clockworkpi/DevTerm/Clockwork_DevTerm_DIY_Graphene_Heat_Sink.pdf

A

+ | =

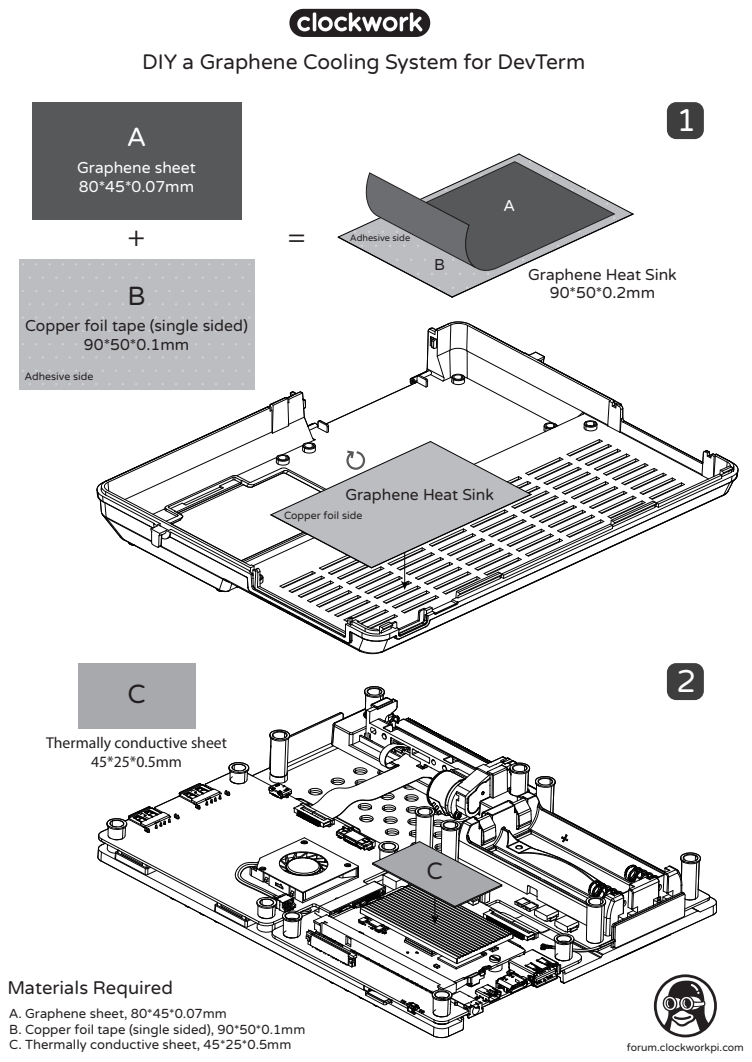
[picture p36: page 1]
Adhesive side; Graphene sheet 80*45*0.07mm; C. Thermally conductive sheet, 45*25*0.5mm; forum.clockworkpi.com

DIY a Graphene Cooling System for DevTerm

Graphene Heat Sink

Copper foil tape (single sided)

Copper foil side

Thermally conductive sheet

Materials Required
A. Graphene sheet, 80*45*0.07mm
B. Copper foil tape (single sided), 90*50*0.1mm
