clockworkpi/DevTerm/Code/thermal_printer/logo.h

#ifndef LOGO_H
#define LOGO_H

#define os120_width 120
#define os120_height 120

const unsigned char os120_bits[] = {
   0x00, 0x00, 0x00, 0x00, 0x00, 0x00, 0x00, 0x00, 0x00, 0x00, 0x00, 0x00,
   0x00, 0x00, 0x00, 0x00, 0x00, 0x00, 0x00, 0x00, 0x00, 0xf8, 0xff, 0x1f,
   0x00, 0x00, 0x00, 0x00, 0x00, 0x00, 0x00, 0x00, 0x00, 0x00, 0x00, 0xc0,
   0xff, 0xff, 0xff, 0x03, 0x00, 0x00, 0x00, 0x00, 0x00, 0x00, 0x00, 0x00,
   0x00, 0x00, 0xfc, 0xff, 0xff, 0xff, 0x3f, 0x00, 0x00, 0x00, 0x00, 0x00,
   0x00, 0x00, 0x00, 0x00, 0x80, 0xff, 0xff, 0xff, 0xff, 0xff, 0x01, 0x00,
   0x00, 0x00, 0x00, 0x00, 0x00, 0x00, 0x00, 0xe0, 0xff, 0xff, 0xff, 0xff,
   0xff, 0x07, 0x00, 0x00, 0x00, 0x00, 0x00, 0x00, 0x00, 0x00, 0xf8, 0xff,
   0x1f, 0x00, 0xf8, 0xff, 0x1f, 0x00, 0x00, 0x00, 0x00, 0x00, 0x00, 0x00,
   0x00, 0xfe, 0x7f, 0x00, 0x00, 0x00, 0xfe, 0x7f, 0x00, 0x00, 0x00, 0x00,
   0x00, 0x00, 0x00, 0x80, 0xff, 0x0f, 0x00, 0x00, 0x00, 0xf0, 0xff, 0x01,
   0x00, 0x00, 0x00, 0x00, 0x00, 0x00, 0xe0, 0xff, 0x01, 0x00, 0x00, 0x00,
   0x80, 0xff, 0x07, 0x00, 0x00, 0x00, 0x00, 0x00, 0x00, 0xf8, 0x3f, 0x00,
   0x00, 0x00, 0x00, 0x00, 0xfc, 0x1f, 0x00, 0x00, 0x00, 0x00, 0x00, 0x00,
   0xfc, 0x0f, 0x00, 0x00, 0x00, 0x00, 0x00, 0xf0, 0x3f, 0x00, 0x00, 0x00,
   0x00, 0x00, 0x00, 0xfe, 0x03, 0x00, 0x00, 0xf8, 0x01, 0x00, 0xc0, 0x7f,
   0x00, 0x00, 0x00, 0x00, 0x00, 0x80, 0xff, 0x01, 0x00, 0xf0, 0xff, 0xff,
   0x00, 0x80, 0xff, 0x01, 0x00, 0x00, 0x00, 0x00, 0xc0, 0x7f, 0x00, 0x00,
   0xff, 0xff, 0xff, 0x07, 0x00, 0xfe, 0x03, 0x00, 0x00, 0x00, 0x00, 0xe0,
   0x1f, 0x00, 0xe0, 0xff, 0xff, 0xff, 0x3f, 0x00, 0xf8, 0x07, 0x00, 0x00,
   0x00, 0x00, 0xf0, 0x0f, 0x00, 0xf8, 0xff, 0xff, 0xff, 0xff, 0x00, 0xf0,
   0x0f, 0x00, 0x00, 0x00, 0x00, 0xf8, 0x07, 0x00, 0xfe, 0xff, 0xff, 0xff,
   0xff, 0x01, 0xe0, 0x1f, 0x00, 0x00, 0x00, 0x00, 0xfc, 0x01, 0x00, 0xff,
   0xff, 0xff, 0xff, 0xff, 0x07, 0x80, 0x3f, 0x00, 0x00, 0x00, 0x00, 0xfe,
   0x00, 0xc0, 0xff, 0xff, 0xff, 0x7f, 0xfc, 0x0f, 0x00, 0x7f, 0x00, 0x00,
   0x00, 0x00, 0x7f, 0x00, 0xe0, 0xff, 0xff, 0xff, 0x3f, 0xf0, 0x1f, 0x00,
   0xfe, 0x00, 0x00, 0x00, 0x80, 0x3f, 0x00, 0xf0, 0xff, 0xff, 0xff, 0x3f,
   0xe0, 0x3f, 0x00, 0xfc, 0x01, 0x00, 0x00, 0xc0, 0x1f, 0x00, 0xf8, 0xff,
   0xff, 0xff, 0x7f, 0x80, 0x7f, 0x00, 0xf8, 0x03, 0x00, 0x00, 0xe0, 0x0f,
   0x00, 0xfc, 0xff, 0xff, 0xff, 0xff, 0x01, 0x7f, 0x00, 0xf0, 0x07, 0x00,
   0x00, 0xe0, 0x07, 0x00, 0xfc, 0xff, 0xff, 0xff, 0xff, 0x07, 0xfe, 0x00,
   0xe0, 0x07, 0x00, 0x00, 0xf0, 0x03, 0x00, 0xfe, 0xff, 0xff, 0xff, 0xff,
   0x0f, 0xfc, 0x01, 0xc0, 0x0f, 0x00, 0x00, 0xf8, 0x03, 0x00, 0xff, 0xff,
   0xff, 0xff, 0xff, 0x1f, 0xfc, 0x01, 0xc0, 0x1f, 0x00, 0x00, 0xfc, 0x01,
   0x00, 0xff, 0xff, 0xff, 0xff, 0xff, 0x3f, 0xf8, 0x03, 0x80, 0x3f, 0x00,
   0x00, 0xfc, 0x00, 0x80, 0xff, 0xff, 0xff, 0xff, 0xff, 0x7f, 0xf0, 0x07,
   0x00, 0x3f, 0x00, 0x00, 0x7e, 0x00, 0x80, 0xff, 0xff, 0xff, 0xff, 0xff,
   0xff, 0xf0, 0x07, 0x00, 0x7e, 0x00, 0x00, 0x7e, 0x00, 0xc0, 0xff, 0xff,
   0xff, 0xff, 0xff, 0xff, 0xf0, 0x07, 0x00, 0x7e, 0x00, 0x00, 0x3f, 0x00,
   0xc0, 0xff, 0xff, 0xff, 0xff, 0xff, 0xff, 0xf9, 0x0f, 0x00, 0xfc, 0x00,
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


#endif
