clockworkpi/DevTerm/Code/thermal_printer/pcf_5x7-ISO8859-1_5x7.h

#ifndef FONT_PCF_5X7_ISO8859_1_5X7_H
#define FONT_PCF_5X7_ISO8859_1_5X7_H

const unsigned char font_pcf_5x7_ISO8859_1_5x7[]   = {

    /*
     * code=0, hex=0x00, ascii="^@"
     */
    0x00,  /* 00000 */
    0xA8,  /* 10101 */
    0x00,  /* 00000 */
    0x88,  /* 10001 */
    0x00,  /* 00000 */
    0xA8,  /* 10101 */
    0x00,  /* 00000 */

    /*
     * code=1, hex=0x01, ascii="^A"
     */
    0x00,  /* 00000 */
    0x20,  /* 00100 */
    0x70,  /* 01110 */
    0xF8,  /* 11111 */
    0x70,  /* 01110 */
    0x20,  /* 00100 */
    0x00,  /* 00000 */

    /*
     * code=2, hex=0x02, ascii="^B"
     */
    0xA8,  /* 10101 */
    0x50,  /* 01010 */
    0xA8,  /* 10101 */
    0x50,  /* 01010 */
    0xA8,  /* 10101 */
    0x50,  /* 01010 */
    0xA8,  /* 10101 */

    /*
     * code=3, hex=0x03, ascii="^C"
     */
    0xA0,  /* 10100 */
    0xE0,  /* 11100 */
    0xA0,  /* 10100 */
    0x70,  /* 01110 */
    0x20,  /* 00100 */
    0x20,  /* 00100 */
    0x00,  /* 00000 */

    /*
     * code=4, hex=0x04, ascii="^D"
     */
    0xE0,  /* 11100 */
    0x80,  /* 10000 */
    0xF8,  /* 11111 */
    0xA0,  /* 10100 */
    0x30,  /* 00110 */
    0x20,  /* 00100 */
    0x00,  /* 00000 */

    /*
     * code=5, hex=0x05, ascii="^E"
     */
    0x60,  /* 01100 */
    0x80,  /* 10000 */
    0xE0,  /* 11100 */
    0x50,  /* 01010 */
    0x60,  /* 01100 */
    0x50,  /* 01010 */
    0x00,  /* 00000 */

    /*
     * code=6, hex=0x06, ascii="^F"
     */
    0x80,  /* 10000 */
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
    0x00,  /* 00000 */
    0xA8,  /* 10101 */
    0x00,  /* 00000 */

    /*
     * code=254, hex=0xFE, ascii="!~"
     */
    0x00,  /* 00000 */
    0xA8,  /* 10101 */
    0x00,  /* 00000 */
    0x88,  /* 10001 */
    0x00,  /* 00000 */
    0xA8,  /* 10101 */
    0x00,  /* 00000 */

    /*
     * code=255, hex=0xFF, ascii="!^Ÿ"
     */
    0x00,  /* 00000 */
    0xA8,  /* 10101 */
    0x00,  /* 00000 */
    0x88,  /* 10001 */
    0x00,  /* 00000 */
    0xA8,  /* 10101 */
    0x00,  /* 00000 */
};

#endif
