clockworkpi/DevTerm/Code/thermal_printer/pcf_6x12-ISO8859-1_6x12.h

#ifndef FONT_PCF_6X12_ISO8859_1_6X12_H
#define FONT_PCF_6X12_ISO8859_1_6X12_H

const unsigned char font_pcf_6x12_ISO8859_1_6x12[] = {

    /*
     * code=0, hex=0x00, ascii="^@"
     */
    0x00,  /* 000000 */
    0x00,  /* 000000 */
    0x00,  /* 000000 */
    0xA8,  /* 101010 */
    0x00,  /* 000000 */
    0x88,  /* 100010 */
    0x00,  /* 000000 */
    0x88,  /* 100010 */
    0x00,  /* 000000 */
    0xA8,  /* 101010 */
    0x00,  /* 000000 */
    0x00,  /* 000000 */

    /*
     * code=1, hex=0x01, ascii="^A"
     */
    0x00,  /* 000000 */
    0x00,  /* 000000 */
    0x00,  /* 000000 */
    0x00,  /* 000000 */
    0x20,  /* 001000 */
    0x70,  /* 011100 */
    0xF8,  /* 111110 */
    0x70,  /* 011100 */
    0x20,  /* 001000 */
    0x00,  /* 000000 */
    0x00,  /* 000000 */
    0x00,  /* 000000 */

    /*
     * code=2, hex=0x02, ascii="^B"
     */
    0xA8,  /* 101010 */
    0x54,  /* 010101 */
    0xA8,  /* 101010 */
    0x54,  /* 010101 */
    0xA8,  /* 101010 */
    0x54,  /* 010101 */
    0xA8,  /* 101010 */
    0x54,  /* 010101 */
    0xA8,  /* 101010 */
    0x54,  /* 010101 */
    0xA8,  /* 101010 */
    0x54,  /* 010101 */

    /*
     * code=3, hex=0x03, ascii="^C"
     */
    0x00,  /* 000000 */
    0xA0,  /* 101000 */
    0xA0,  /* 101000 */
    0xE0,  /* 111000 */
    0xA0,  /* 101000 */
    0xB8,  /* 101110 */
    0x10,  /* 000100 */
    0x10,  /* 000100 */
    0x10,  /* 000100 */
    0x10,  /* 000100 */
    0x00,  /* 000000 */
    0x00,  /* 000000 */

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
    0x00,  /* 000000 */
    0x00,  /* 000000 */
    0xA8,  /* 101010 */
    0x00,  /* 000000 */
    0x88,  /* 100010 */
    0x00,  /* 000000 */
    0x88,  /* 100010 */
    0x00,  /* 000000 */
    0xA8,  /* 101010 */
    0x00,  /* 000000 */
    0x00,  /* 000000 */
};

#endif
