clockworkpi/DevTerm/Code/thermal_printer/pcf_7x14-ISO8859-1_7x14.h

#ifndef FONT_PCF_7X14_ISO8859_1_7X14_H
#define FONT_PCF_7X14_ISO8859_1_7X14_H

const unsigned char font_pcf_7x14_ISO8859_1_7x14[] = {

    /*
     * code=0, hex=0x00, ascii="^@"
     */
    0x00,  /* 0000000 */
    0xB4,  /* 1011010 */
    0x84,  /* 1000010 */
    0x00,  /* 0000000 */
    0x84,  /* 1000010 */
    0x84,  /* 1000010 */
    0x00,  /* 0000000 */
    0x84,  /* 1000010 */
    0x84,  /* 1000010 */
    0x00,  /* 0000000 */
    0x84,  /* 1000010 */
    0xB4,  /* 1011010 */
    0x00,  /* 0000000 */
    0x00,  /* 0000000 */

    /*
     * code=1, hex=0x01, ascii="^A"
     */
    0x00,  /* 0000000 */
    0x00,  /* 0000000 */
    0x30,  /* 0011000 */
    0x30,  /* 0011000 */
    0x78,  /* 0111100 */
    0x78,  /* 0111100 */
    0xFC,  /* 1111110 */
    0xFC,  /* 1111110 */
    0x78,  /* 0111100 */
    0x78,  /* 0111100 */
    0x30,  /* 0011000 */
    0x30,  /* 0011000 */
    0x00,  /* 0000000 */
    0x00,  /* 0000000 */

    /*
     * code=2, hex=0x02, ascii="^B"
     */
    0x54,  /* 0101010 */
    0xAA,  /* 1010101 */
    0x54,  /* 0101010 */
    0xAA,  /* 1010101 */
    0x54,  /* 0101010 */
    0xAA,  /* 1010101 */
    0x54,  /* 0101010 */
    0xAA,  /* 1010101 */
    0x54,  /* 0101010 */
    0xAA,  /* 1010101 */
    0x54,  /* 0101010 */
    0xAA,  /* 1010101 */
    0x54,  /* 0101010 */
    0xAA,  /* 1010101 */

    /*
     * code=3, hex=0x03, ascii="^C"
     */
    0x00,  /* 0000000 */
    0x90,  /* 1001000 */
    0x90,  /* 1001000 */
    0xF0,  /* 1111000 */
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
    0x00,  /* 0000000 */
    0x84,  /* 1000010 */
    0x84,  /* 1000010 */
    0x00,  /* 0000000 */
    0x84,  /* 1000010 */
    0x84,  /* 1000010 */
    0x00,  /* 0000000 */
    0x84,  /* 1000010 */
    0xB4,  /* 1011010 */
    0x00,  /* 0000000 */
    0x00,  /* 0000000 */
};

#endif
