clockworkpi/DevTerm/Code/thermal_printer/ttf_Px437_PS2thin1_8x16.h

#ifndef FONT_TTF_PX437_PS2THIN1_8X16_H
#define FONT_TTF_PX437_PS2THIN1_8X16_H

const unsigned char font_ttf_Px437_PS2thin1_8x16[] = {

    /*
     * code=0, hex=0x00, ascii="^@"
     */
    0x00,  /* 00000000 */
    0x00,  /* 00000000 */
    0x00,  /* 00000000 */
    0x00,  /* 00000000 */
    0x00,  /* 00000000 */
    0x00,  /* 00000000 */
    0x00,  /* 00000000 */
    0x00,  /* 00000000 */
    0x00,  /* 00000000 */
    0x00,  /* 00000000 */
    0x00,  /* 00000000 */
    0x00,  /* 00000000 */
    0x00,  /* 00000000 */
    0x00,  /* 00000000 */
    0x00,  /* 00000000 */
    0x00,  /* 00000000 */

    /*
     * code=1, hex=0x01, ascii="^A"
     */
    0x00,  /* 00000000 */
    0x00,  /* 00000000 */
    0x00,  /* 00000000 */
    0x00,  /* 00000000 */
    0x7C,  /* 01111100 */
    0x82,  /* 10000010 */
    0xAA,  /* 10101010 */
    0x82,  /* 10000010 */
    0xBA,  /* 10111010 */
    0x92,  /* 10010010 */
    0x82,  /* 10000010 */
    0x7C,  /* 01111100 */
    0x00,  /* 00000000 */
    0x00,  /* 00000000 */
    0x00,  /* 00000000 */
    0x00,  /* 00000000 */

    /*
     * code=2, hex=0x02, ascii="^B"
     */
    0x00,  /* 00000000 */
    0x00,  /* 00000000 */
    0x00,  /* 00000000 */
    0x00,  /* 00000000 */
    0x7C,  /* 01111100 */
    0xFE,  /* 11111110 */
    0xD6,  /* 11010110 */
    0xFE,  /* 11111110 */
    0xFE,  /* 11111110 */
    0xC6,  /* 11000110 */
    0xEE,  /* 11101110 */
    0x7C,  /* 01111100 */
    0x00,  /* 00000000 */
    0x00,  /* 00000000 */
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
    0x44,  /* 01000100 */
    0x82,  /* 10000010 */
    0xFE,  /* 11111110 */
    0x82,  /* 10000010 */
    0x44,  /* 01000100 */
    0x38,  /* 00111000 */
    0x00,  /* 00000000 */
    0x00,  /* 00000000 */
    0x00,  /* 00000000 */
    0x00,  /* 00000000 */
    0x00,  /* 00000000 */

    /*
     * code=186, hex=0xBA, ascii="!:"
     */
    0x00,  /* 00000000 */
    0x00,  /* 00000000 */
    0x00,  /* 00000000 */
    0xFE,  /* 11111110 */
    0x82,  /* 10000010 */
    0x40,  /* 01000000 */
    0x20,  /* 00100000 */
    0x10,  /* 00010000 */
    0x20,  /* 00100000 */
    0x40,  /* 01000000 */
    0x82,  /* 10000010 */
    0xFE,  /* 11111110 */
    0x00,  /* 00000000 */
    0x00,  /* 00000000 */
    0x00,  /* 00000000 */
    0x00,  /* 00000000 */
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
